D4VI365/SimPedals/CAD/3D Printed/NormalSpacer.step

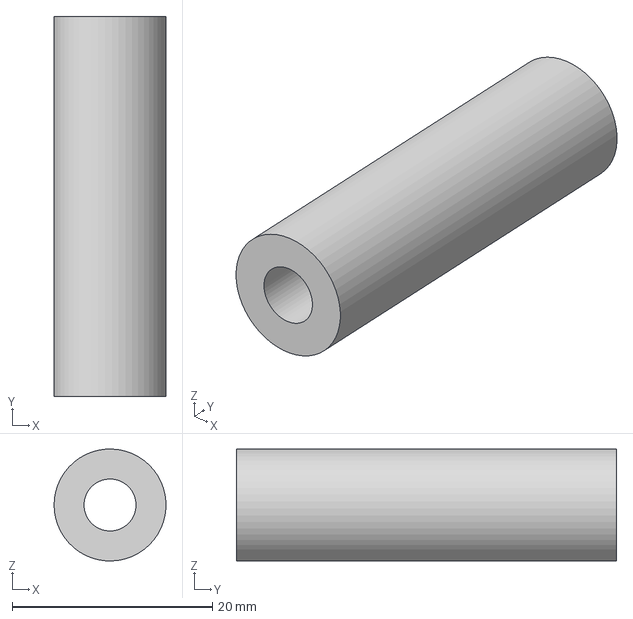
[picture p19: CAD file, 2026-06-30]
CAD/3D Printed/NormalSpacer.step
11.2 x 38.0 x 11.2 mm
