D4VI365/SimPedals/CAD/Metal Plate/SpringSupportFlat.step

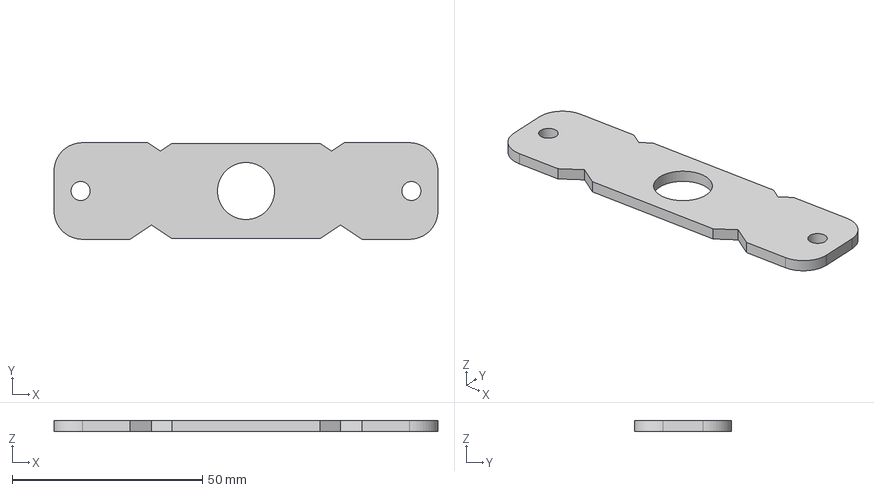
[picture p20: CAD file, 2026-06-30]
CAD/Metal Plate/SpringSupportFlat.step
101.0 x 25.4 x 3.00 mm
