D4VI365/SimPedals/CAD/3D Printed/PedalPlateHolder.step

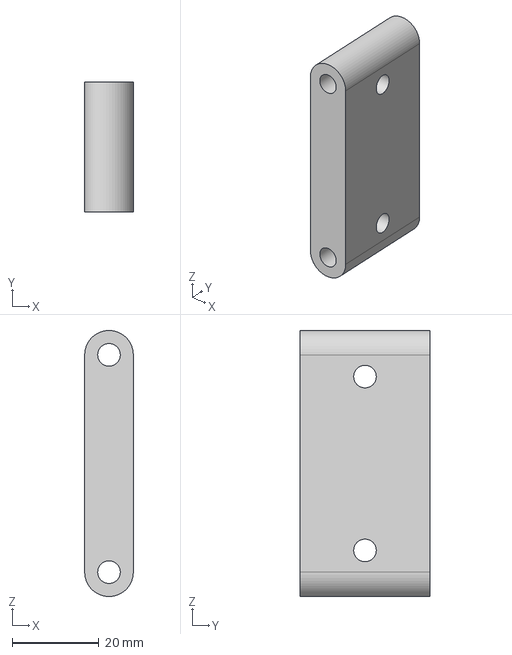
[picture p21: CAD file, 2026-06-30]
CAD/3D Printed/PedalPlateHolder.step
11.2 x 30.0 x 61.2 mm
