D4VI365/SimPedals/CAD/Metal Plate/LoadCellTransmission.step

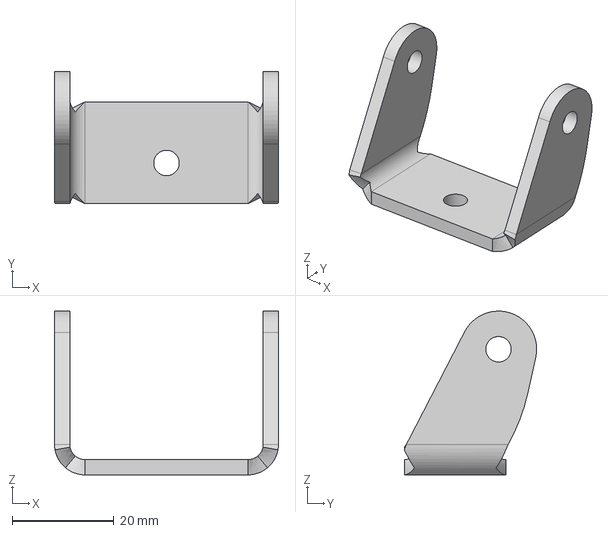
[picture p22: CAD file, 2026-06-30]
CAD/Metal Plate/LoadCellTransmission.step
44.0 x 26.0 x 32.2 mm
