D4VI365/SimPedals/CAD/Metal Plate/LaodCellHolder.step

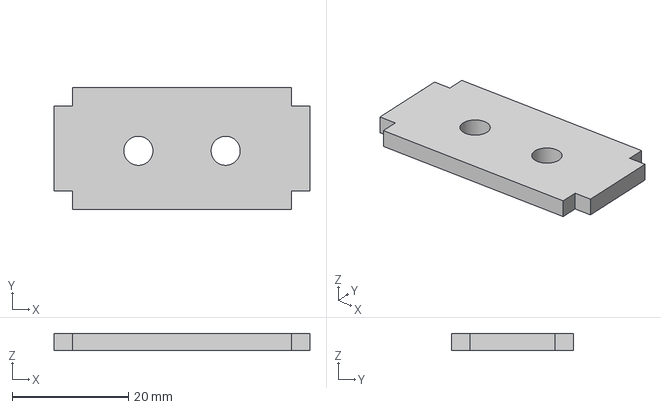
[picture p23: CAD file, 2026-06-30]
CAD/Metal Plate/LaodCellHolder.step
44.0 x 21.0 x 3.00 mm
