D4VI365/SimPedals/CAD/Metal Plate/AcceleratorPlate.step

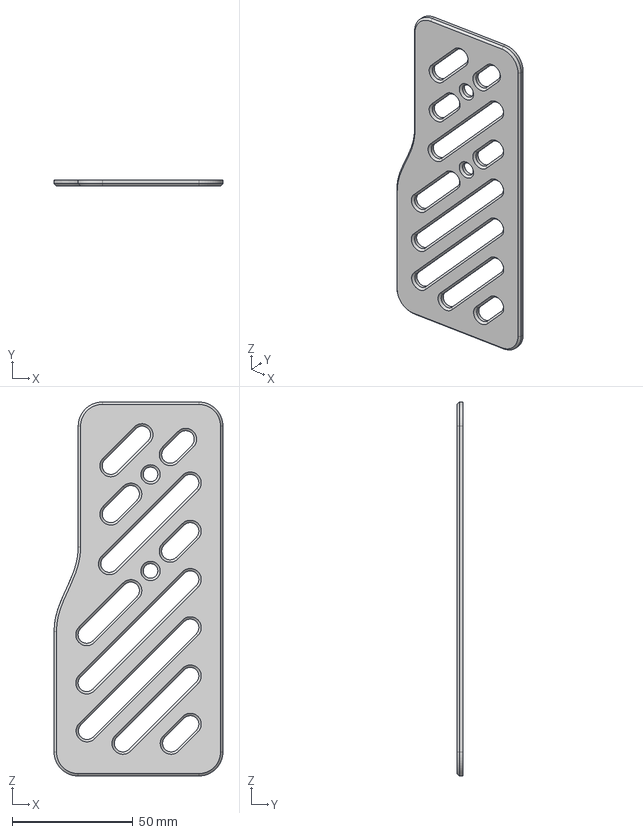
[picture p24: CAD file, 2026-06-30]
CAD/Metal Plate/AcceleratorPlate.step
70.0 x 2.50 x 155.0 mm
