D4VI365/SimPedals/CAD/Metal Plate/SidePlateFlat.step

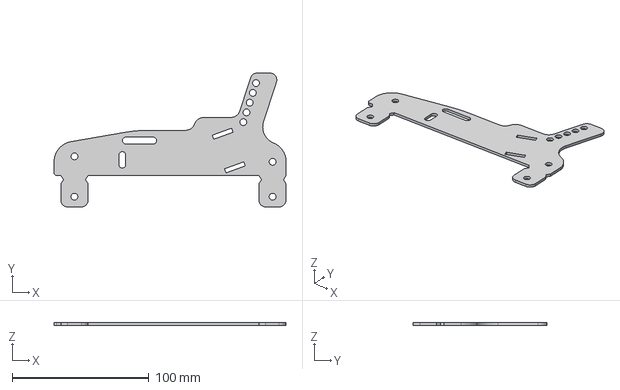
[picture p25: CAD file, 2026-06-30]
CAD/Metal Plate/SidePlateFlat.step
169.8 x 98.0 x 2.00 mm
